JNSRYA006/EEE4113F_Camera_Trap/Base Station/db code/Images_db_schema.png

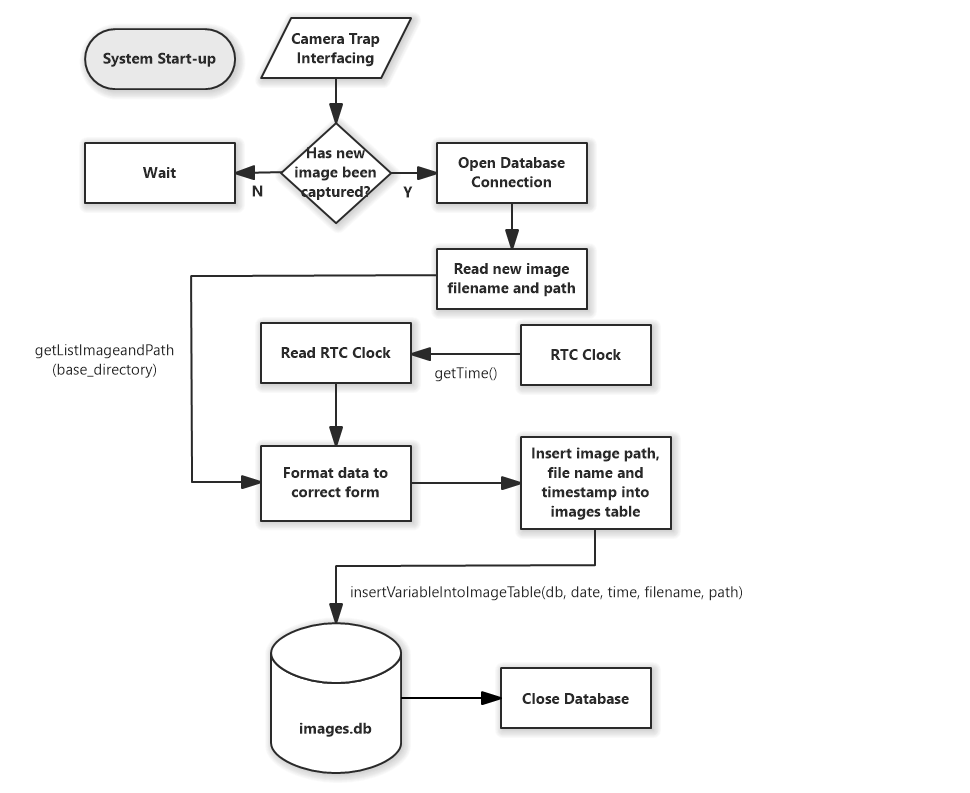
Base Station/db code/Images_db_schema.png
