JNSRYA006/EEE4113F_Camera_Trap/Base Station/Housing/Housing_image_4.png

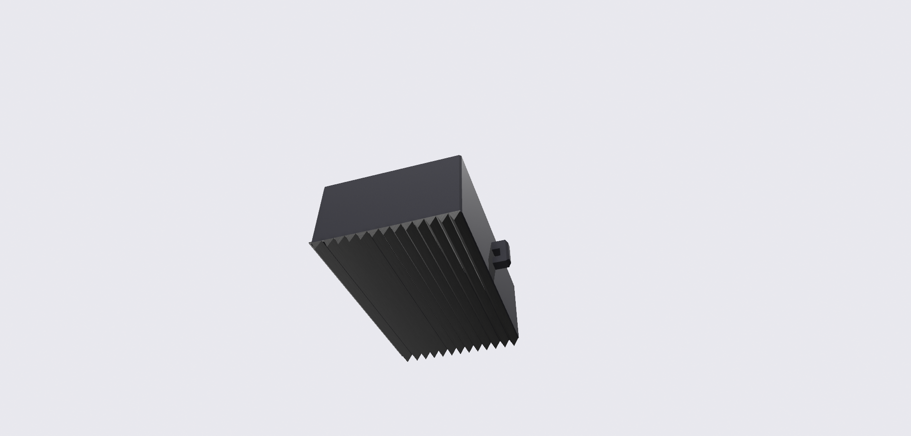
Base Station/Housing/Housing_image_4.png
